Recycling-Werkstatt-insel-eV/Nistkasten_1_Oskar/CNC_milling/CNC_milling_Documentation/detail1.png

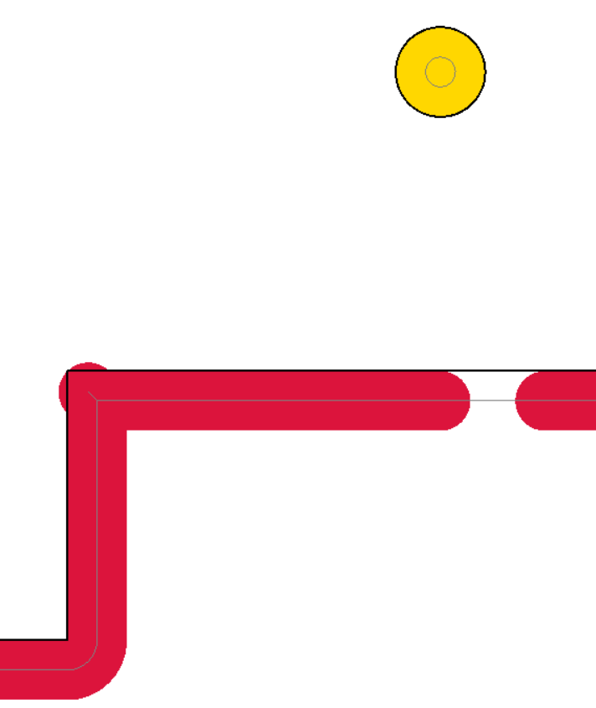
CNC_milling/CNC_milling_Documentation/detail1.png
